nickgeoca/elata-eeg/crates/sensors/src/eeg_system/mod.rs

use std::error::Error;
use tokio::sync::mpsc;
use tokio::task::JoinHandle;
use std::time::Duration;
use tokio_util::sync::CancellationToken;

use crate::board_drivers::{
    create_driver, AdcConfig, AdcData, AdcDriver, DriverError, DriverEvent, DriverStatus, DriverType,
};

pub struct EegSystem {
    driver: Box<dyn AdcDriver>,
    processing_task: Option<JoinHandle<()>>,
    tx: mpsc::Sender<AdcData>,
    event_rx: Option<mpsc::Receiver<DriverEvent>>,
    cancel_token: CancellationToken,
}

impl EegSystem {
    /// Creates an EEG processing system without starting it
    pub async fn new(
        config: AdcConfig
    ) -> Result<(Self, mpsc::Receiver<AdcData>), Box<dyn Error>> {
        let (driver, event_rx) = create_driver(config.clone()).await?;
        let (tx, rx) = mpsc::channel(100);
        let cancel_token = CancellationToken::new();

        let system = Self {
            driver,
            processing_task: None,
            tx,
            event_rx: Some(event_rx),
            cancel_token,
        };

        Ok((system, rx))
    }

    /// Starts the processing system with the given configuration
    pub async fn start(&mut self, config: AdcConfig) -> Result<(), Box<dyn Error>> {
        self.initialize_processing(config).await
    }

    /// Internal helper to initialize or reinitialize the driver and processing task
    async fn initialize_processing(&mut self, config: AdcConfig) -> Result<(), Box<dyn Error>> {
        // Add validation before proceeding
        if config.channels.is_empty() {
            return Err(Box::new(DriverError::ConfigurationError(
                "Cannot initialize with zero channels".into()
            )));
        }

        if config.sample_rate == 0 {
            return Err(Box::new(DriverError::ConfigurationError(
                "Sample rate must be greater than 0".into()
            )));
        }

        // Cancel any existing processing task gracefully
        if self.processing_task.is_some() {
            self.cancel_token.cancel();
            // Create a new token for the next task
            self.cancel_token = CancellationToken::new();
        }
 
        // // Reset the signal processor // Removed as per DSP refactor plan
        // {
        //     let mut proc_guard = match self.processor.lock().await {
        //         guard => guard,
        //         // This would only happen if a thread panicked while holding the lock
        //         // In a real system, we might want to recreate the processor entirely
        //     };
            
        //     proc_guard.reset(
        //         config.sample_rate,
        //         config.channels.len(),
        //         config.dsp_high_pass_cutoff_hz,
        //         config.dsp_low_pass_cutoff_hz,
        //         config.powerline_filter_hz
        //     );
        // }

        self.driver.start_acquisition().await?;

        // Take ownership of the event receiver
        let mut event_rx = self.event_rx.take().expect("Event receiver should exist");

        // Start the processing task
        let tx = self.tx.clone();
        // Clone the cancellation token for the task
        let cancel_token = self.cancel_token.clone();

        self.processing_task = Some(tokio::spawn(async move {
            // Create a select future that will complete when either:
            // 1. We receive an event from the driver
            // 2. The cancellation token is triggered
            loop {
                tokio::select! {
                    // Check if cancellation was requested
                    _ = cancel_token.cancelled() => {
                        break;
                    }
                    // Process events from the driver
                    event_opt = event_rx.recv() => {
                        match event_opt {
                            Some(event) => {
                                match event {
                                    DriverEvent::Data(data_batch) => {
                                        // Forward each AdcData directly to the output channel
                                        for data in data_batch {
                                            if let Err(e) = tx.send(data).await {
                                                eprintln!("Error sending data: {}", e);
                                                // Continue processing - don't break on send errors
                                            }
                                        }
                                    }
                                    DriverEvent::StatusChange(status) => {
                                        if status == DriverStatus::Stopped {
                                            break;
                                        }
                                        
                                        // Log status changes but don't forward them
                                        println!("Driver status changed: {:?}", status);
                                    }
                                    DriverEvent::Error(err_msg) => {
                                        eprintln!("Driver error: {}", err_msg);
                                        // Note: We can't send errors through AdcData channel
                                        // Errors will be handled by the device daemon
                                    }
                                }
                            }
                            None => {
                                // Channel closed, exit the task
                                break;
                            }
                        }
                    }
                }
            }
        }));

        Ok(())
    }


    /// Stop the data acquisition & gracefully cancel the background task
    pub async fn stop(&mut self) -> Result<(), Box<dyn Error>> {
        self.driver.stop_acquisition().await?;
        
        // Signal the task to stop gracefully
        if self.processing_task.is_some() {
            self.cancel_token.cancel();
            
            // Wait for a short time for the task to complete
            if let Some(task) = self.processing_task.take() {
                match tokio::time::timeout(Duration::from_millis(500), task).await {
                    Ok(_) => {
                        // Task completed gracefully
                    },
                    Err(_) => {
                        // Task didn't complete in time, force abort
                        // This is a fallback mechanism
                        eprintln!("Warning: Processing task didn't complete in time, forcing abort");
                    }
                }
            }
            
            // Create a new token for future tasks
            self.cancel_token = CancellationToken::new();
        }
        
        Ok(())
    }

    /// Reconfigure the driver with new settings, resetting the processor
    pub async fn reconfigure(&mut self, config: AdcConfig) -> Result<(), Box<dyn Error>> {
        // Stop the current driver and processing task
        self.stop().await?;
        
        // Create a new driver with the updated configuration
        let (new_driver, new_event_rx) = create_driver(config.clone()).await?;
        
        // Replace the driver and event_rx
        self.driver = new_driver;
        self.event_rx = Some(new_event_rx);
        
        // Initialize processing with the new configuration
        self.initialize_processing(config).await
    }

    /// Retrieve the current driver status
    pub async fn driver_status(&self) -> DriverStatus {
        self.driver.get_status().await
    }

    /// Retrieve the driver's configuration
    pub async fn driver_config(&self) -> Result<AdcConfig, DriverError> {
        self.driver.get_config().await
    }

    /// Optionally allow direct driver access
    pub fn driver(&mut self) -> &mut Box<dyn AdcDriver> {
        &mut self.driver
    }

    /// Completely shut down the EEG system and clean up resources
    pub async fn shutdown(&mut self) -> Result<(), Box<dyn Error>> {
        // Add timeout for safety
        const SHUTDOWN_TIMEOUT_MS: u64 = 1000;
        
        let shutdown_future = async {
            // Convert the Box<dyn Error> to DriverError
            if let Err(e) = self.stop().await {
                return Err(DriverError::Other(e.to_string()));
            }
            self.driver.shutdown().await
        };
        
        match tokio::time::timeout(
            Duration::from_millis(SHUTDOWN_TIMEOUT_MS),
            shutdown_future
        ).await {
            Ok(result) => result.map_err(|e| Box::new(e) as Box<dyn Error>),
            Err(_) => Err(Box::new(DriverError::Other("Shutdown timed out".into())))
        }
    }
}

impl Drop for EegSystem {
    fn drop(&mut self) {
        // Since we can't use .await in Drop, we'll just log a warning
        eprintln!("Warning: EegSystem dropped without calling shutdown() first");
        eprintln!("Always call system.shutdown().await before dropping the system");
    }
}
