nickgeoca/elata-eeg/crates/sensors/src/ads1299/mod.rs

//! ADS1299 driver for interfacing with the ADS1299EEG_FE board.
//!
//! This module provides a driver for the ADS1299 analog-to-digital converter,
//! which is commonly used in EEG applications.

// Re-export the driver module for backward compatibility
pub mod driver;

// Test module
pub mod test;

// New modules
pub mod error;
pub mod helpers;
pub mod registers;
pub mod spi;

// Re-export the main driver struct and builder for convenience
pub use driver::Ads1299Driver;
