nickgeoca/elata-eeg/driver/src/board_driver/mod.rs

pub mod mock_driver;
pub mod mock_data_generator;
pub mod ads1299_driver;
pub mod types;

// Re-export types for convenience
pub use self::types::{AdcData, AdcConfig, DriverEvent, DriverStatus, DriverError, AdcDriver, DriverType};
pub use self::mock_driver::MockDriver;
pub use self::ads1299_driver::Ads1299Driver;
pub use self::types::create_driver;
